spandanb10745/FMCW-radar-for-Object-Detection/Images/Amplifier.png

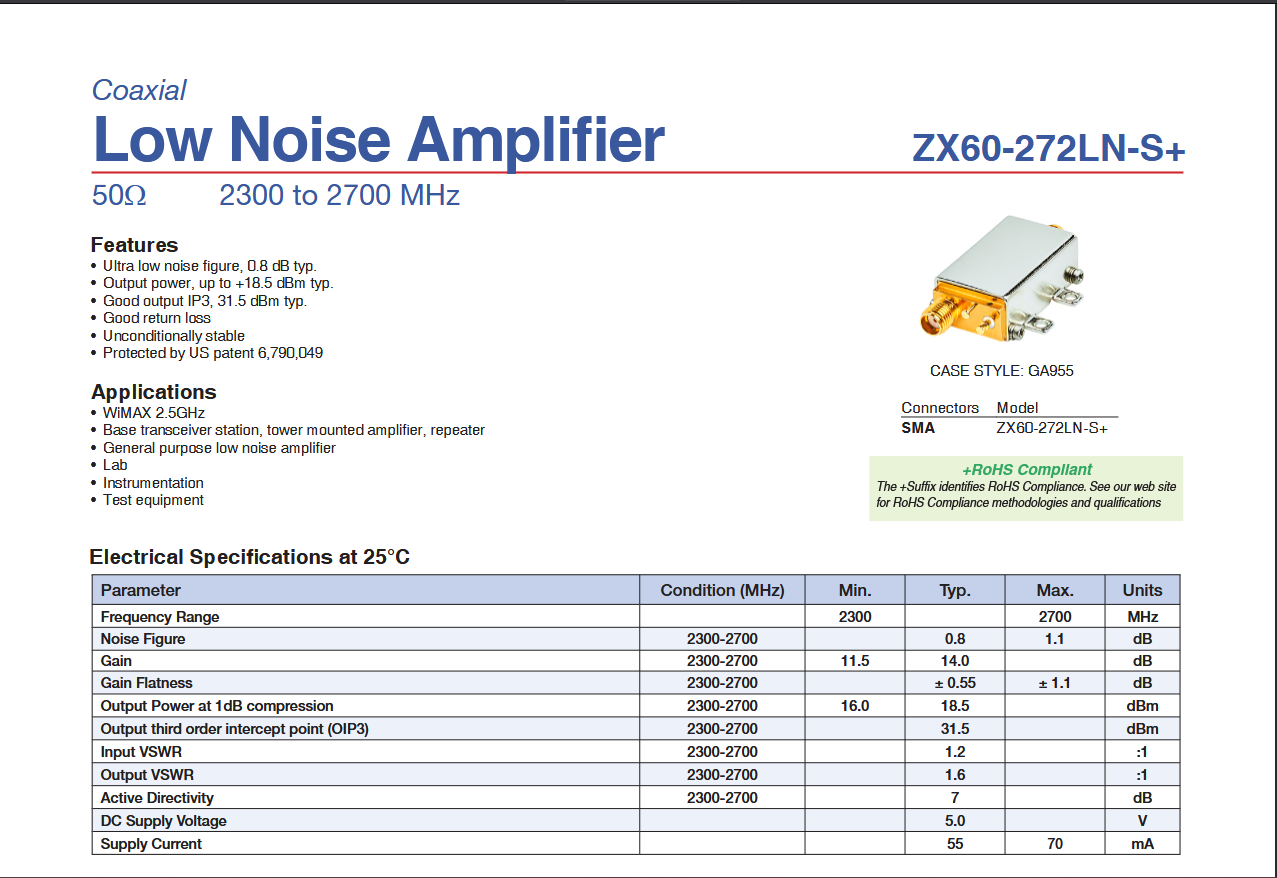
Images/Amplifier.png
