spandanb10745/FMCW-radar-for-Object-Detection/Images/Oscillator.png

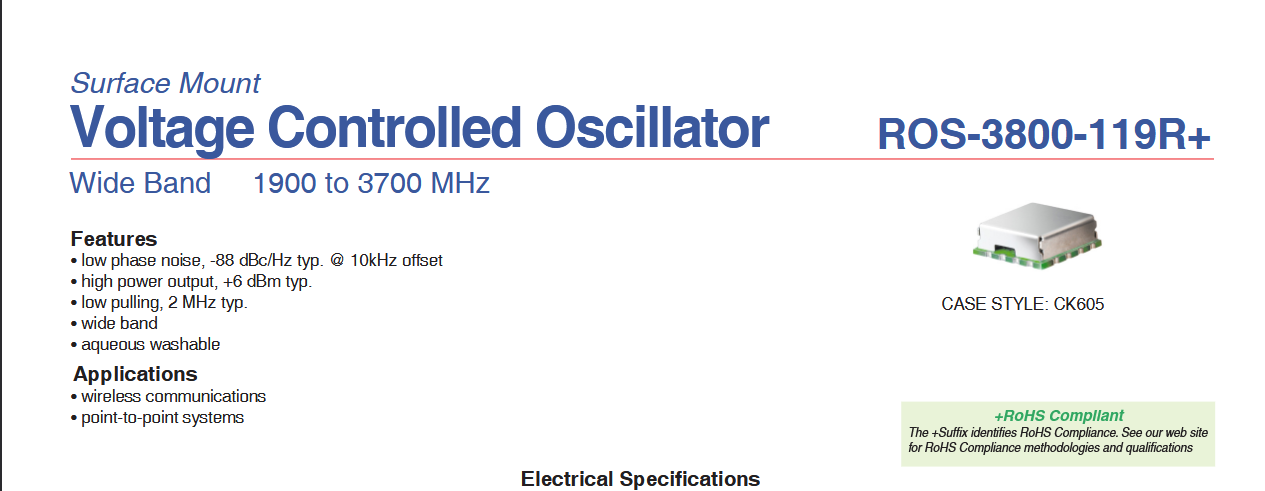
Images/Oscillator.png
