spandanb10745/FMCW-radar-for-Object-Detection/Images/Oscillator_data_sheet.png

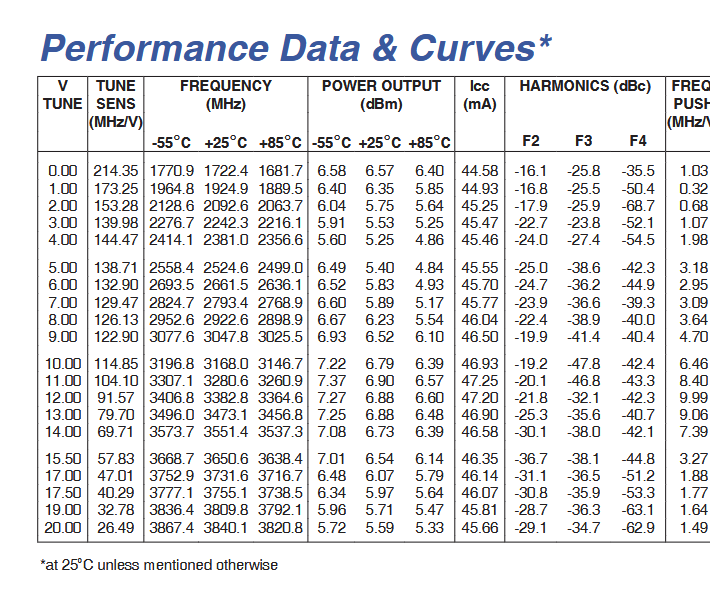
Images/Oscillator_data_sheet.png
