spandanb10745/FMCW-radar-for-Object-Detection/Images/Splitter.png

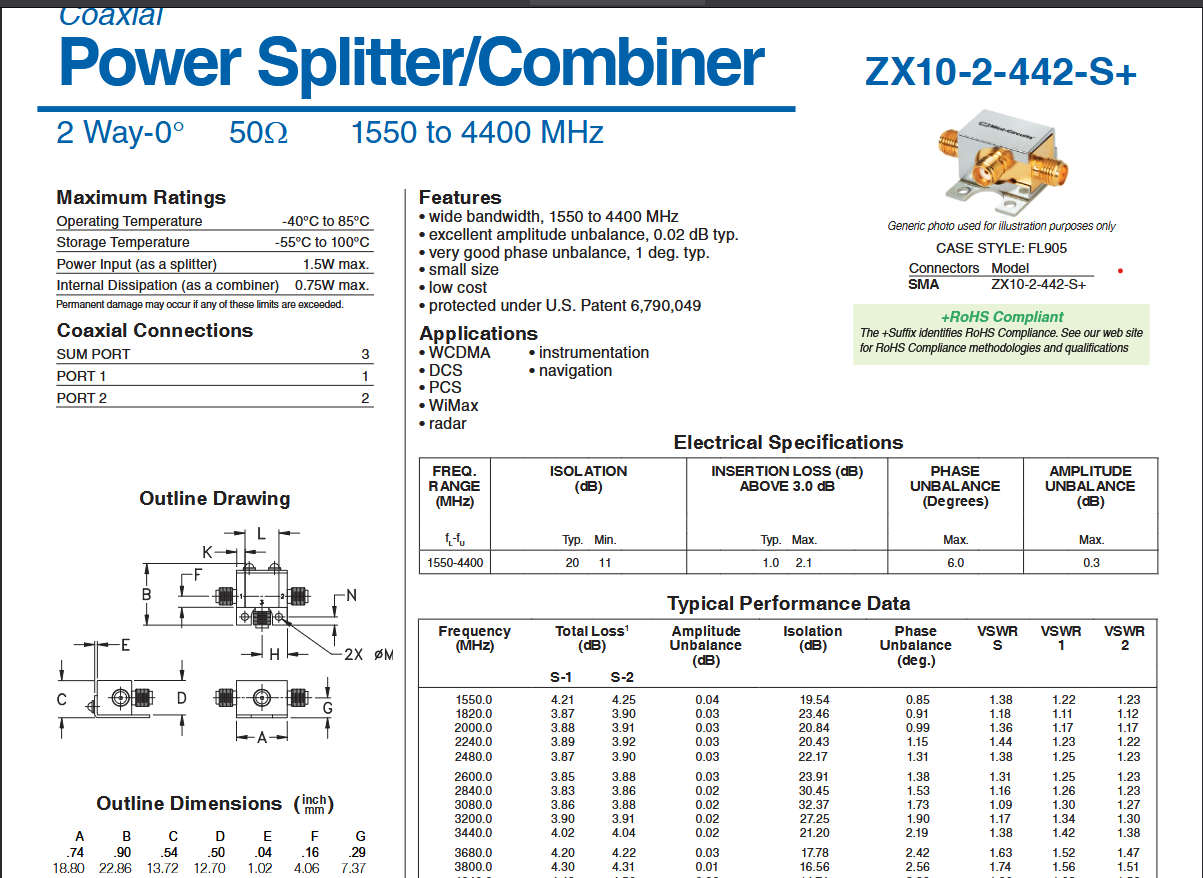
Images/Splitter.png
